ElliotLard/nrf52-co2-sensor/hardware/datasheets/MDBT50 & MDBT50-P Footprint & Design Guide (221129)/2D & 3D Drawing/MDBT50/3D/MDBT50-3.jpg

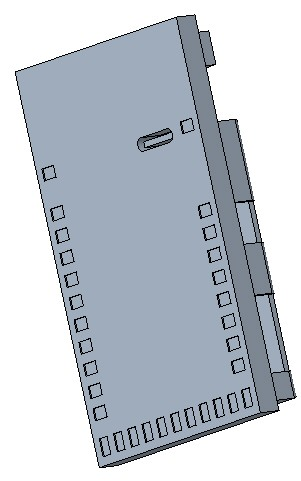
hardware/datasheets/MDBT50 & MDBT50-P Footprint & Design Guide (221129)/2D & 3D Drawing/MDBT50/3D/MDBT50-3.jpg
