ElliotLard/nrf52-co2-sensor/hardware/datasheets/MDBT50 & MDBT50-P Footprint & Design Guide (221129)/Footprint (nRF52820)_MDBT50-256R & P256R/MDBT50 Eagle Library/MDBT50_52820 Eagle Library-210706.jpg

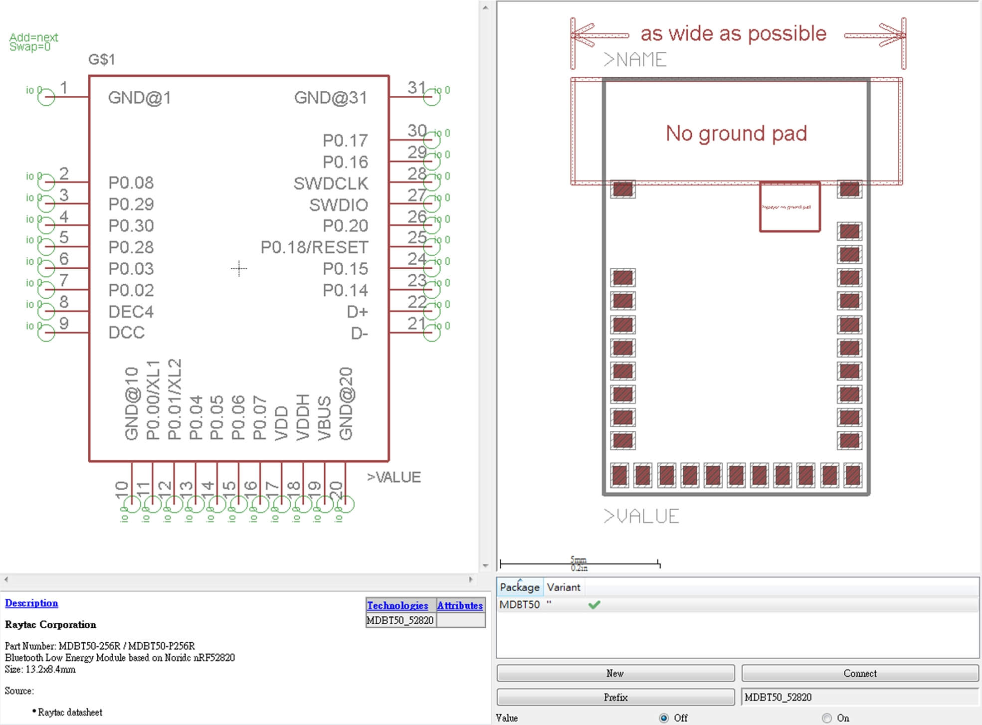
hardware/datasheets/MDBT50 & MDBT50-P Footprint & Design Guide (221129)/Footprint (nRF52820)_MDBT50-256R & P256R/MDBT50 Eagle Library/MDBT50_52820 Eagle Library-210706.jpg
