ElliotLard/nrf52-co2-sensor/hardware/datasheets/MDBT50 & MDBT50-P Footprint & Design Guide (221129)/Footprint (nRF52833)_MDBT50-512K & P512K/MDBT50 Eagle Library/MDBT50_52833 Eagle Library-210706.jpg

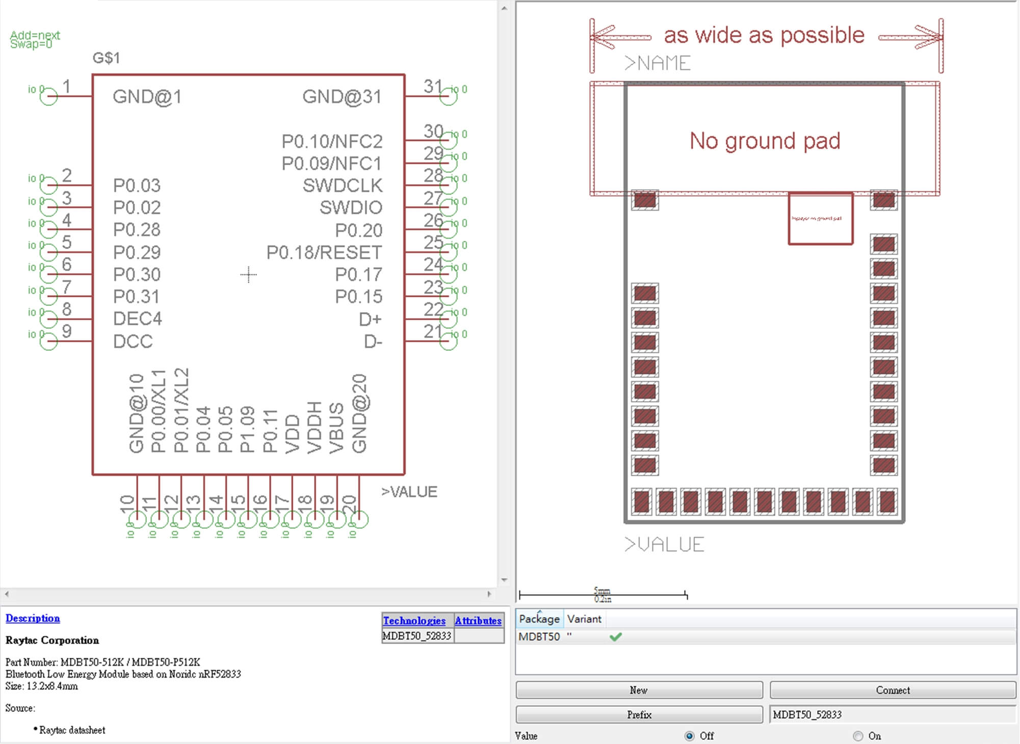
hardware/datasheets/MDBT50 & MDBT50-P Footprint & Design Guide (221129)/Footprint (nRF52833)_MDBT50-512K & P512K/MDBT50 Eagle Library/MDBT50_52833 Eagle Library-210706.jpg
